dabonetn/Link232-Wifi/zimodem/cbm8bit/src/irc-sw64.bas

!--------------------------------------------------
!- Tuesday, August 17, 2021 9:45:22 AM
!- Import of : 
!- z:\lost+found\irc.prg
!- Commodore 64
!--------------------------------------------------
1 REM IRC64SW  19200B 1.8+
2 REM UPDATED 10/13/2021 12:54A
10 POKE254,PEEK(186):IFPEEK(254)<8THENPOKE254,8
12 GOSUB9200:IFSY=61THENPOKE58,254:CLR
13 IFSY=34THENX=23777:POKEX,170:IFPEEK(X)<>170THENPRINT"<16k":STOP
14 IFSY=227ANDPEEK(51201)=3THENSYS51200
15 OPEN5,2,0,CHR$(BC):IFPEEK(65532)=34THENPOKE56,87:POKE54,87:POKE52,87
17 DIMPP$(25):P$="ok":POKE186,PEEK(254):BA=1200:XB=1200
20 CR$=CHR$(13):PRINTCHR$(14);:GOSUB9200:POKE53280,254:POKE53281,246
30 CO$="{light blue}":IFSY=226THENML=49152:POKE665,73-(PEEK(678)*30):UM=ML+2048:XB=9600
33 IFSY=227THENML=49152:UM=ML+2048
35 IFSY=34THENML=22273:IFPEEK(ML)<>76THENCLOSE5:LOAD"pmlvic.bin",PEEK(254),1:RUN
38 IFSY=34THENPOKE36879,27:CO$=CHR$(31)
40 IFSY=226ANDPEEK(ML+1)<>209THENCLOSE5:LOAD"pml64.bin",PEEK(254),1:RUN
43 IFSY=227ANDPEEK(ML+1)<>209THENCLOSE5:LOAD"pml64.bin",PEEK(254),1:RUN
44 IFSY=227ANDPEEK(51201)<>3THENCLOSE5:LOAD"swiftdrvr.bin",PEEK(254),1:RUN
45 IFSY=226ANDUM>0ANDPEEK(UM+1)<>24THENCLOSE5:LOAD"up9600.bin",PEEK(254),1:RUN
50 IFSY=61THENML=4864:POKE981,15:S8=PEEK(215)AND128:IFS8=128THENSYS30643
60 IFSY=61ANDPEEK(ML+1)<>217THENCLOSE5:LOAD"pml128.bin",PEEK(254),1:RUN
70 IFSY=61ANDS8=128THENXB=2400:CO$=CHR$(159)
80 IFSY=226ANDUM>0THENSYSUM:SYSUM+3:X=PEEK(789):SYSUM+9:IFX=234THENXB=1200
90 IFSY<>34THENPOKE56579,0:REM WHY DOES THIS WORK
100 REM GET THE BAUD RATE
110 P$="a"
120 PRINTCO$;"{clear}{down*2}IRC CHAT v1.5":PRINT"Requires Zimodem firmware 1.8+"
140 PRINT"By Bo Zimmerman (bo@zimmers.net)":PRINT:PRINT
197 REM --------------------------------
198 REM GET STARTED                    !
199 REM -------------------------------
200 UN=PEEK(254):IP$="":CR$=CHR$(13)+CHR$(10)
201 PH=0:PT=0:MV=ML+18
202 PRINT "Initializing modem..."
203 GET#5,A$:IFA$<>""THEN203
205 PRINT#5,CR$;"athz0&p0f0e0";CR$;:GOSUB900:IFP$<>"ok"THEN203
208 GET#5,A$:IFA$<>""THEN208
210 PRINT#5,CR$;"ate0n0r0v1q0";CR$;
220 GOSUB900:IFP$<>"ok"THEN208
230 PRINT#5,"ate0v1x1f3q0s40=250i4";CR$;CHR$(19);
235 GOSUB900:VR=VAL(P$):IFVR<1.8THENPRINT"Zimodem init failed: ";P$:STOP
240 GOSUB900:IFP$<>"ok"THEN203
300 REM GET THE SERVER
310 PRINT:PRINT"{down}Some servers:"
320 PRINT"irc.nlnog.net port 6667, #c-64"
325 PRINT"irc.freenode.net port 6667, #c64friends"
330 PRINT"irc.us.ircnet.net port 6667, #c-64"
350 SE$="":PRINT:PRINT"What is your IRC server host":GOSUB5000:SE$=P$
360 IFSE$=""THENPRINT"I guess you're done then":CLOSE5:STOP
370 PRINT"What is the port":GOSUB5000:PO$=P$:IFVAL(PO$)<=0THENSE$="":GOTO360
380 SE$=SE$+":"+PO$
390 GET#5,A$:IFA$<>""THEN390
400 REM MAKE THE CONNECTION
405 AT$="":IFXB>0ANDBA>0ANDXB<>BATHENAT$="s43="+MID$(STR$(XB),2)
406 GET#5,A$:IFA$<>""THEN406
410 QU$=CHR$(34):PRINT#5,"at"+AT$+"h&d13&m13&m10cp";QU$;SE$;QU$
415 GOSUB900
420 IFLEFT$(P$,8)<>"connect "THENPRINT"Unable to connect to ";SE$;":";P$:GOTO300
425 P=VAL(MID$(P$,8))
427 IFXB<>9600THEN430
428 SYSUM:SYSUM+3:IFPEEK(789)=234THENSYSUM+9:GOTO435
429 BA=XB:POKEUM+19,1:PRINT#5,"at":GOSUB9000:GOSUB9000
430 IFXB<>2400THEN435
431 NP=0:IFPEEK(2614)>0THENNP=20
432 BA=XB:POKE2576,10:POKE2578,PEEK(59490+NP):POKE2579,PEEK(59491+NP)
433 POKE2582,170:POKE2583,1:IFNP>0THENPOKE2582,154
435 PRINT#5,"at":GOSUB9000:GOSUB9000
440 PRINT:PRINT"What is your nickname";:GOSUB5000:NI$=P$:N1=LEN(NI$)
450 IFNI$=""THENPRINT"I guess not.":STOP
460 P$="NICK "+NI$:GOSUB600
470 P$="USER guest 0 * :Joe Anonymous":GOSUB600
490 PRINT"{light green}{reverse on}Connected, wait for MOTD. ? for help{reverse off}";CO$
500 GOTO 1000: REM GO START MAIN LP
598 REM --- TRANSMIT P$ TO THE OPEN SOCKET
600 IFLEN(P$)>0ANDASC(RIGHT$(P$,1))=10THENP$=LEFT$(P$,LEN(P$)-1)
605 OP$=P$:SYSML+9:C8$=MID$(STR$(PEEK(MV+8)),2)::E$="ok":IFVR>3THENE$=C8$
610 PRINT#5,"ats42=";C8$;"t+";QU$;P$;QU$
620 SYSML:IFP$<>E$THENP$=OP$:PRINT"xmit fail";CC$:GOTO600
630 RETURN
698 REM --- GET NEXT FROM SOCKET INTO PP
700 GOSUB930:IFP0<>PANDP0>0THENPRINT"Unexpected packet id: ";P0;"/";P:STOP
710 IFP0=0THENRETURN
720 PP$(PE)=P$:PE=PE+1:IFPE>=25THENPE=0
790 P$="":RETURN
798 REM --- GET P$ FROM SOCKET P
800 E=0:P$="":IFPH>=25THENPH=0
810 IFPH<>PETHENP$=PP$(PH):PH=PH+1:RETURN
820 GOSUB700:IFP0=0THENE=1:RETURN:REM FAIL
830 IFPH<>PETHENP$=PP$(PH):PH=PH+1:RETURN
840 E=1:RETURN
898 REM ---- GET E$ FROM MODEM, OR ERROR
900 E$=""
910 SYSML
920 IFE$<>""ANDP$<>E$THENPRINT"{reverse on}{red}Comm error. Expected ";E$;", Got ";P$;CO$;"{reverse off}"
925 RETURN
928 REM GET PACKET HEADER, SETS P0,P1,P2, RETURNS P0=0 IF NADA
930 SYSML+12:E=0:P0=0:P1=0:P2=0:PR=0:I=0:I0=0:I1=0:CR=0:P4=0:P5=0:C8=0
940 P$="":PRINT#5,CHR$(17);
945 SYSML+6:P0=PEEK(MV+2):P1=PEEK(MV+4):P2=PEEK(MV+6)
950 PL=PEEK(MV+0):CR=PEEK(MV+1):C8=PEEK(MV+8)
960 IFP0>0ANDP2<>C8THEN985
970 IFP1=0THENP$=""
980 IFP0>0ORCR=0THENRETURN
985 SYSML+12:P$=""
990 PRINT"{yellow}PACKET-RETRY";CO$:PRINT#5,"atl":GOTO945
995 PRINT"Expected ";E$;", got ";A$:STOP
998 REM THE MAIN LOOP
1000 GETA$:IFA$<>""THEN3000
1020 GOSUB800:IFP$=""THEN1000
1030 MS$="":MC$="":MA$="":I=1:LP$=P$
1040 IFMID$(P$,1,1)<>":"THEN1100
1050 IFI>LEN(P$)THEN1100
1060 IFMID$(P$,I,1)<>" "THENI=I+1:GOTO1050
1070 MS$=MID$(P$,1,I-1):P$=MID$(P$,I+1)
1100 I=1:IFP$=""THEN1000
1110 IFI>LEN(P$)THEN1200
1120 IFMID$(P$,I,1)<>" "THENI=I+1:GOTO1110
1130 MC$=MID$(P$,1,I-1):P$=MID$(P$,I+1)
1200 MA$=P$:IFMC$=""THEN1000
1210 A=ASC(MID$(MC$,1,I)):IFA<48ORA>57THEN1300
1220 IFLEN(MC$)>1ANDMID$(MC$,1,1)="0"THENMC$=MID$(MC$,2):GOTO1220
1230 C=VAL(MC$):IFC>430ANDC<460THENPRINT"Bad Nick given(";C;") : "+MA$:GOTO440
1240 IFC>400THENPRINT"Error: "+MA$:GOTO1000
1250 IFLEN(MA$)>N1+1ANDMID$(MA$,1,N1)=NI$THENMA$=MID$(MA$,LEN(NI$)+2)
1260 PRINT MA$:GOTO1000
1300 REM CMDS
1310 IFMC$="PING"THEN1400
1320 IFMC$="MODE"THEN1000
1330 IFMC$="PRIVMSG"THEN2000
1340 IFMC$="VERSION"THEN2100
1350 IFMC$="QUIT"THEN2200
1360 IFMC$="JOIN"THEN2300
1370 IFMC$="PONG"THEN1000
1390 REM
1397 PRINTLP$:GOTO1000
1398 PRINT"Unknown: '"+MC$+"' '"+MA$+"'"
1399 GOTO1000
1400 REM ...
1410 OM$=MA$:P$="PONG :"+MA$:GOSUB600:E$="":GOTO1000
2000 I=1:IFMA$=""THEN1000
2010 IFMID$(MA$,I,2)=" :"THEN2050
2020 I=I+1:GOTO2010
2050 GOSUB2900
2090 PRINT"{reverse on}";MS$;"{reverse off}: ";MID$(MA$,I+2):GOTO1000
2100 PRINT"{reverse on}";LP$;"{reverse off}":GOTO1000
2200 GOSUB2900:PRINT"{pink}{reverse on}";MS$;" has left the channel.{reverse off}";CO$:GOTO1000
2300 GOSUB2900:PRINT"{light green}{reverse on}";MS$;" has joined the channel.{reverse off}";CO$:GOTO1000
2900 II=2
2910 IFII>LEN(MS$)THENII=LEN(MS$):GOTO2950
2920 IFMID$(MS$,II,1)="!"THENII=II-1:GOTO2950
2930 II=II+1:GOTO2910
2950 MS$=MID$(MS$,1,II):RETURN
3000 IFA$=CHR$(13)THEN1000
3010 PRINT"{reverse on}{pink}Stream paused. Enter ? for help.{reverse off}"
3020 IFOM$<>""THENP$="PING "+OM$:GOSUB600
3090 PRINTCO$;">{reverse on} {reverse off}{left}";:IN$="":IT=TI+1000:GOTO3200
3100 IFTI>ITTHENPRINT"{reverse on}{red}Cancelled{reverse off}{pink}":PRINT:GOTO1000
3150 GETA$:IFA$=""THEN3100
3170 IT=TI+1000
3200 IFA$=CHR$(13)THEN3300
3210 IFA$<>CHR$(20)ORLEN(IN$)=0THEN3230
3220 IN$=LEFT$(IN$,LEN(IN$)-1):PRINT" {left*2} {left}{reverse on} {reverse off}{left}";:GOTO3100
3230 A=ASC(A$):IFA<32OR(A>95ANDA<193)ORA>218THEN3100
3240 IN$=IN$+A$:PRINTA$;"{reverse on} {reverse off}{left}";:GOTO3100
3300 IFIN$=""THENPRINT" ":PRINT:GOTO1000
3305 IFIN$="?"THENPRINT" ":GOTO3400
3310 IFMID$(IN$,1,1)="/"THENIN$=MID$(IN$,2):GOTO3500
3320 IFCC$=""THENPRINT:PRINT"{reverse on}{red}No Channel Selected! Try ?{reverse off}";CO$:GOTO1000
3330 P$="PRIVMSG "+CC$+" :"+IN$
3340 GOSUB600:PRINT" ":PRINT"{reverse on}";NI$;"{reverse off}: ";IN$
3350 E$="":PRINT:GOTO1000
3400 PRINTCO$;"{reverse off}------------------------------"
3410 PRINT"{reverse on}{purple}/join #c-64{reverse off} ";CO$;"Change channels."
3420 PRINT"{reverse on}{purple}/quit{reverse off} ";CO$;"Logout and exit."
3430 REMPRINT"{reverse on}{purple}/list{reverse off} ";CO$;"List channels."
3440 REMPRINT"{reverse on}{purple}/who mask*{reverse off} ";CO$;"User info."
3480 PRINT"{reverse on}{purple}Anything else{reverse off} ";CO$;"Send message"
3490 PRINTCO$;"{reverse off}------------------------------":GOTO1000
3500 X=0:FORI=2TOLEN(IN$):IFX=0ANDMID$(IN$,I,1)=" "THENX=I
3510 NEXT:A$="":IFX>1THENA$=MID$(IN$,X+1):IN$=MID$(IN$,1,X-1)
3520 PRINT
3530 IFIN$="join"THEN4000
3540 IFIN$="quit"THENP$="QUIT :":GOSUB600:GOTO9100
3550 IFIN$="list"THENP$="LIST":GOSUB600:GOTO1000
3560 IFIN$="who"THENP$="WHO :"+AA$:GOSUB600:GOTO1000
3999 PRINT"{reverse on}{red}Unknown Command: ";IN$;". Try ?{reverse off}";CO$:GOTO1000
4000 PRINT"Joining ";QU$;A$;QU$:AA$=A$
4100 P$="JOIN :"+AA$:GOSUB600
4120 E$="":CC$=AA$:GOTO1000
5000 PRINT"? {reverse on} {reverse off}{left}";:P$=""
5010 GETA$:IFA$=""THEN5010
5020 IFA$=CHR$(13)THENPRINT" {left}":RETURN
5030 IFA$<>CHR$(20)THENPRINTA$;"{reverse on} {reverse off}{left}";:P$=P$+A$:GOTO5010
5040 IFP$=""THEN5010
5050 P$=LEFT$(P$,LEN(P$)-1):PRINT" {left*2} {left}{reverse on} {reverse off}{left}";:GOTO5010
9000 TT=TI+100
9010 SYSML+12:IFTI<TTTHEN9010
9020 RETURN
9100 PRINT#5,"atz":GOSUB9000:GOSUB9000:CLOSE5:END
9200 SY=PEEK(65532):BC=8
9210 IFSY<>226THEN9240
9220 X=PEEK(56834):POKE56834,X+1:IFPEEK(56834)<>X+1THEN9240
9230 BC=15:SY=227:POKE56834,X:RETURN
9240 PRINTCHR$(14);"Requires a C64 with SwiftLink/Link232":STOP
50000 OPEN5,2,0,CHR$(8)
50010 GET#5,A$:IFA$<>""THENPRINTA$;
50020 GETA$:IFA$<>""THENPRINT#5,A$;
50030 GOTO 50010
55555 U=8:F$="irc":OPEN1,U,15,"s0:"+F$:CLOSE1:SAVEF$,U:VERIFYF$,U
