dabonetn/Link232-Wifi/zimodem/zimodem/zprint.ino

/*
   Copyright 2020-2020 Bo Zimmerman

   Licensed under the Apache License, Version 2.0 (the "License");
   you may not use this file except in compliance with the License.
   You may obtain a copy of the License at

     http://www.apache.org/licenses/LICENSE-2.0

   Unless required by applicable law or agreed to in writing, software
   distributed under the License is distributed on an "AS IS" BASIS,
   WITHOUT WARRANTIES OR CONDITIONS OF ANY KIND, either express or implied.
   See the License for the specific language governing permissions and
   limitations under the License.
*/

size_t ZPrint::writeStr(char *s)
{
  if(outStream != null)
  {
    int len=strlen(s);
    outStream->write((uint8_t *)s,len);
    if(logFileOpen)
    {
      for(int i=0;i<len;i++)
        logSocketOut(s[i]);
    }
    return len;
  }
  return 0;
}

char *ZPrint::getLastPrinterSpec()
{
  if(lastPrinterSpec==0)
    return "";
  return lastPrinterSpec;
}

void ZPrint::setLastPrinterSpec(const char *spec)
{
  if(lastPrinterSpec != 0)
    free(lastPrinterSpec);
  lastPrinterSpec = 0;
  if((spec != 0) && (*spec != 0))
  {
    int newLen = strlen(spec);
    lastPrinterSpec = (char *)malloc(newLen + 1);
    strcpy(lastPrinterSpec,spec);
  }
}


int ZPrint::getTimeoutDelayMs()
{
  return timeoutDelayMs;
}

void ZPrint::setTimeoutDelayMs(int ms)
{
  if(ms > 50)
    timeoutDelayMs = ms;
}

size_t ZPrint::writeChunk(char *s, int len)
{
  char buf[25];
  sprintf(buf,"%x\r\n",len);
  writeStr(buf);
  outStream->write((uint8_t *)s,len);
  if(logFileOpen)
  {
    for(int i=0;i<len;i++)
      logSocketOut(s[i]);
  }
  writeStr("\r\n");
  return len+strlen(buf)+4;
}

void ZPrint::announcePrintJob(const char *hostIp, const int port, const char *req)
{
  logPrintfln("Print Request to host=%s, port=%d",hostIp,port);
  debugPrintf("Print Request to host=%s, port=%d\n",hostIp,port);
  logPrintfln("Print Request is /%s",req);
  debugPrintf("Print Request is /%s\n",req);
}

ZResult ZPrint::switchToPostScript(char *prefix)
{
  if((lastPrinterSpec==0)
  ||(strlen(lastPrinterSpec)<=5)
  ||(lastPrinterSpec[1]!=':'))
    return ZERROR;
  char *workBuf = (char *)malloc(strlen(lastPrinterSpec) +1);
  strcpy(workBuf, lastPrinterSpec);
  
  char *hostIp;
  char *req;
  int port;
  bool doSSL;
  if(!parseWebUrl((uint8_t *)workBuf+2,&hostIp,&req,&port,&doSSL))
  {
    free(workBuf);
    return ZERROR;
  }
  payloadType = RAW;
  announcePrintJob(hostIp,port,req);
  ZResult result;
  if(pinSupport[pinRTS])
    s_pinWrite(pinRTS, rtsInactive);
  yield();
  wifiSock = new WiFiClientNode(hostIp,port,doSSL?FLAG_SECURE:0);
  wifiSock->setNoDelay(false); // we want a delay in this case
  outStream = wifiSock;
  result = finishSwitchTo(hostIp, req, port, doSSL);
  if(result == ZERROR)
  {
    outStream = null;
    delete wifiSock;
    wifiSock = null;
  }
  yield();
  if(pinSupport[pinRTS])
    s_pinWrite(pinRTS, rtsActive);
  if((result != ZERROR)
  &&(prefix != 0)
  &&(strlen(prefix)>0))
  {
    writeChunk(prefix,strlen(prefix));
    serialIncoming();
  }
  free(workBuf);
  return result;
}

ZResult ZPrint::switchTo(char *vbuf, int vlen, bool petscii)
{
  char *workBuf = (char *)malloc(vlen+1);
  strcpy(workBuf, vbuf);
  if(petscii)
  {
    for(int i=0;i<vlen;i++)
      workBuf[i] = petToAsc(workBuf[i]);
  }
  bool newUrl = true;
  if((vlen <= 2)||(workBuf[1]!=':'))
  {
    if((lastPrinterSpec==0)
    ||(strlen(lastPrinterSpec)<=5)
    ||(lastPrinterSpec[1]!=':'))
    {
      free(workBuf);
      return ZERROR;
    }
    if((vlen == 1)
    &&(strchr("parPAR",workBuf[0])!=0))
      lastPrinterSpec[0]=workBuf[0];
    free(workBuf);
    workBuf = (char *)malloc(strlen(lastPrinterSpec) +1);
    strcpy(workBuf, lastPrinterSpec);
    vlen=strlen(workBuf);
    newUrl = false;
  }
  
  switch(workBuf[0])
  {
  case 'P': case 'p': 
    payloadType = PETSCII;
    break;
  case 'A': case 'a': 
    payloadType = ASCII;
    break;
  case 'R': case 'r': 
    payloadType = RAW;
    break;
  default:
    free(workBuf);
    return ZERROR;
  }
  char *hostIp;
  char *req;
  int port;
  bool doSSL;
  if(!parseWebUrl((uint8_t *)workBuf+2,&hostIp,&req,&port,&doSSL))
  {
    free(workBuf);
    return ZERROR;
  }
  if(newUrl)
    setLastPrinterSpec(vbuf);
  
  wifiSock = new WiFiClientNode(hostIp,port,doSSL?FLAG_SECURE:0);
  wifiSock->setNoDelay(false); // we want a delay in this case
  outStream = wifiSock;
  announcePrintJob(hostIp,port,req);
  ZResult result = finishSwitchTo(hostIp, req, port, doSSL);
  free(workBuf);
  if(result == ZERROR)
    delete wifiSock;
  return result;
}

ZResult ZPrint::finishSwitchTo(char *hostIp, char *req, int port, bool doSSL)
{
  if((wifiSock != null) && (!wifiSock->isConnected()))
    return ZERROR;
  char portStr[10];
  sprintf(portStr,"%d",port);
  // send the request and http headers:
  sprintf(pbuf,"POST /%s HTTP/1.1\r\n",req);
  writeStr(pbuf);
  writeStr("Transfer-Encoding: chunked\r\n");
  writeStr("Content-Type: application/ipp\r\n");
  sprintf(pbuf,"Host: %s:%d\r\n",hostIp,port);
  writeStr(pbuf);
  writeStr("Connection: Keep-Alive\r\n");
  writeStr("User-Agent: Zimodem\r\n");
  writeStr("Accept-Encoding: gzip,deflate\r\n");
  writeStr("\r\n");
  outStream->flush();
  // send the ipp header
  if((wifiSock != null)&&(!wifiSock->isConnected()))
    return ZERROR;
  
  char jobChar1 = '0' + (jobNum / 10);
  char jobChar2 = '0' + (jobNum % 10);
  if(++jobNum>94)
    jobNum=0;
  //                                version  operatid  reqid------------------ attribtabid
  sprintf(pbuf,"%c%c%c%c%c%c%c%c%c",0x01,0x01,0x00,0x02,0x00,0x00,0x00,jobNum+1,0x01);
  writeChunk(pbuf,9);
  sprintf(pbuf,"%c%c%cattributes-charset%c%cutf-8",0x47,0x00,0x12,0x00,0x05);
  writeChunk(pbuf,28);
  sprintf(pbuf,"%c%c%cattributes-natural-language%c%cen-us",0x48,0x00,0x1b,0x00,0x05);
  writeChunk(pbuf,37);
  
  int urllen = strlen(hostIp) + strlen(req)+ strlen(portStr)+9;
  sprintf(pbuf,"%c%c%cprinter-uri%c%chttp://%s:%s/%s",0x45,0x00,0x0b,0x00,urllen,hostIp,portStr,req);
  writeChunk(pbuf,urllen+16);
  sprintf(pbuf,"%c%c%crequesting-user-name%c%czimodem",0x42,0x00,0x14,0x00,0x07);
  writeChunk(pbuf,32);
  sprintf(pbuf,"%c%c%cjob-name%c%czimodem-j%c%c",0x42,0x00,0x08,0x00,0x0b,jobChar1,jobChar2);
  writeChunk(pbuf,24);
  sprintf(pbuf,"%c%c%c%ccopies%c%c%c%c%c%c",0x02,0x21,0x00,0x06,0x00,0x04,0x00,0x00,0x00,0x01);
  writeChunk(pbuf,16);
  sprintf(pbuf,"%c%c%corientation-requested%c%c%c%c%c%c",0x23,0x00,0x15,0x00,0x04,0x00,0x00,0x00,0x03);
  writeChunk(pbuf,30);
  sprintf(pbuf,"%c%c%coutput-mode%c%cmonochrome%c",0x44,0x00,0x0b,0x00,0x0a,     0x03);
  writeChunk(pbuf,27);
  outStream->flush();
  if((wifiSock != null)&&(!wifiSock->isConnected()))
    return ZERROR;
  checkOpenConnections();
  checkBaudChange();
  pdex=0;
  coldex=0;
  lastNonPlusTimeMs = 0;
  plussesInARow=0;
  currentExpiresTimeMs = millis()+5000;
  currMode=&printMode;
  return ZIGNORE;
}

void ZPrint::serialIncoming()
{
  if(HWSerial.available() > 0)
  {
    while(HWSerial.available() > 0)
    {
      uint8_t c=HWSerial.read();
      logSerialIn(c);
      if((c==commandMode.EC)
      &&(plussesInARow<3)
      &&((plussesInARow>0)||((millis()-lastNonPlusTimeMs)>900)))
      {
        plussesInARow++;
        continue;
      }
      else
      {
        if(plussesInARow > 0)
        {
          for(int i=0;i<plussesInARow;i++)
            pbuf[pdex++]=commandMode.EC;
          plussesInARow=0;
        }
        lastNonPlusTimeMs=millis();
      }
      
      if(payloadType == PETSCII)
        c=petToAsc(c);
      if(payloadType != RAW)
      {
        if(c==0)
          continue;
        else
        if(c<32)
        {
          if((c=='\r')||(c=='\n'))
          {
            coldex=0;
          }
        }
        else
        {
          coldex++;
          if(coldex > 80)
          {
            pbuf[pdex++]='\n';
            pbuf[pdex++]='\r';
            coldex=1;
          }
          else
          if((lastC == '\n')&&(lastLastC!='\r'))
              pbuf[pdex++]='\r';
          else
          if((lastC == '\r')&&(lastLastC!='\n'))
              pbuf[pdex++]='\n';
        }
      }
      pbuf[pdex++]=(char)c;
      lastLastC=lastC;
      lastC=c;
      if(pdex>=250)
      {
        if(((wifiSock!=null)&&(wifiSock->isConnected()))
        ||((wifiSock==null)&&(outStream!=null)))
        {
          writeChunk(pbuf,pdex);
          //wifiSock->flush();
        }
        pdex=0;
      }
    }
    if(plussesInARow == 3)
      currentExpiresTimeMs = millis()+900;
    else
      currentExpiresTimeMs = millis()+timeoutDelayMs;
  }
}

void ZPrint::switchBackToCommandMode(bool error)
{
  if((wifiSock != null)||(outStream!=null))
  {
    if(error)
      commandMode.sendOfficialResponse(ZERROR);
    else
      commandMode.sendOfficialResponse(ZOK);
    if(wifiSock != null)
      delete wifiSock;
  }
  wifiSock = null;
  outStream = null;
  currMode = &commandMode;
}

void ZPrint::loop()
{
  if(((wifiSock==null)&&(outStream==null))
  || ((wifiSock!=null)&&(!wifiSock->isConnected())))
  {
    debugPrintf("No printer connection\n");
    switchBackToCommandMode(true);
  }
  else
  if(millis()>currentExpiresTimeMs)
  {
    debugPrintf("Time-out in printing\n");
    if(pdex > 0)
      writeChunk(pbuf,pdex);
    writeStr("0\r\n\r\n");
    outStream->flush();
    switchBackToCommandMode(false);
  }
  checkBaudChange();
}
