dabonetn/Link232-Wifi/zimodem/cbm8bit/src/x-xfer128.asm

*= $C800
;.D X-XFER128.BIN
; Requires modem on channel 5, file on channel 2
        JMP SENDFIL
        JMP RECVCHK
        JMP SENDFIL
        JMP RECVCRC
PRINT2
        NOP
        ;OPEN1,8,15,"S0:X-XFER 1300,ML1300X":CLOSE1:SAVE"ML1300X",8:STOP
;**********
;CRC TABLES
;**********
CRCLSB
        BYTE 0,33,66,99,132,165,198,231
        BYTE 8,41,74,107,140,173,206,239
        BYTE 49,16,115,82,181,148,247,214
        BYTE 57,24,123,90,189,156,255,222
        BYTE 98,67,32,1,230,199,164,133
        BYTE 106,75,40,9,238,207,172,141
        BYTE 83,114,17,48,215,246,149,180
        BYTE 91,122,25,56,223,254,157,188
        BYTE 196,229,134,167,64,97,2,35
        BYTE 204,237,142,175,72,105,10,43
        BYTE 245,212,183,150,113,80,51,18
        BYTE 253,220,191,158,121,88,59,26
        BYTE 166,135,228,197,34,3,96,65
        BYTE 174,143,236,205,42,11,104,73
        BYTE 151,182,213,244,19,50,81,112
        BYTE 159,190,221,252,27,58,89,120
        BYTE 136,169,202,235,12,45,78,111
        BYTE 128,161,194,227,4,37,70,103
        BYTE 185,152,251,218,61,28,127,94
        BYTE 177,144,243,210,53,20,119,86
        BYTE 234,203,168,137,110,79,44,13
        BYTE 226,195,160,129,102,71,36,5
        BYTE 219,250,153,184,95,126,29,60
        BYTE 211,242,145,176,87,118,21,52
        BYTE 76,109,14,47,200,233,138,171
        BYTE 68,101,6,39,192,225,130,163
        BYTE 125,92,63,30,249,216,187,154
        BYTE 117,84,55,22,241,208,179,146
        BYTE 46,15,108,77,170,139,232,201
        BYTE 38,7,100,69,162,131,224,193
        BYTE 31,62,93,124,155,186,217,248
        BYTE 23,54,85,116,147,178,209,240
;
CRCMSB
        BYTE 0,16,32,48,64,80,96,112
        BYTE 129,145,161,177,193,209,225,241
        BYTE 18,2,50,34,82,66,114,98
        BYTE 147,131,179,163,211,195,243,227
        BYTE 36,52,4,20,100,116,68,84
        BYTE 165,181,133,149,229,245,197,213
        BYTE 54,38,22,6,118,102,86,70
        BYTE 183,167,151,135,247,231,215,199
        BYTE 72,88,104,120,8,24,40,56
        BYTE 201,217,233,249,137,153,169,185
        BYTE 90,74,122,106,26,10,58,42
        BYTE 219,203,251,235,155,139,187,171
        BYTE 108,124,76,92,44,60,12,28
        BYTE 237,253,205,221,173,189,141,157
        BYTE 126,110,94,78,62,46,30,14
        BYTE 255,239,223,207,191,175,159,143
        BYTE 145,129,177,161,209,193,241,225
        BYTE 16,0,48,32,80,64,112,96
        BYTE 131,147,163,179,195,211,227,243
        BYTE 2,18,34,50,66,82,98,114
        BYTE 181,165,149,133,245,229,213,197
        BYTE 52,36,20,4,116,100,84,68
        BYTE 167,183,135,151,231,247,199,215
        BYTE 38,54,6,22,102,118,70,86
        BYTE 217,201,249,233,153,137,185,169
        BYTE 88,72,120,104,24,8,56,40
        BYTE 203,219,235,251,139,155,171,187
        BYTE 74,90,106,122,10,26,42,58
        BYTE 253,237,221,205,189,173,157,141
        BYTE 124,108,92,76,60,44,28,12
        BYTE 239,255,207,223,175,191,143,159
        BYTE 110,126,78,94,46,62,14,30
;****************
;VARIABLE STORAGE
;****************
BUFFER = $CEFD
BUFFER3 = $CF00
ENDBUF = $CF80
CRCBUF = $CF81
ACK = $06
CAN = $18
EOT = $04
NAK = $15
SOH = $01
CNAK = $43
PAD = $1A
OTH = $02


ABORTFLAG = $FB
UPDN = $FE
XTYPE = $FF
FREEKEY = $FA


; KERNAL JUMPS
JSRFAR = $02CD
LOCJSRFAR = $1BE0
FETCH = $02A2

; C128 Specific Locations
TIMEHB = $A0
TIMEMB = $A1
TIMELB = $A2
SHFLAG = $D3
RIDBS = $0A18 ; index to first char in input buffer
RIDBE = $0A19 ; index to last char in input buffer
RODBS = $0A1A ; index to first char in output buffer
RODBE = $0A1B ; index to last char in output buffer
KEYINDEX = $D0
CASSSYNCCT = $96
STATUS = $90
RIBUF = $C8

;***************
;VARIABLE MEMORY
;***************
BLOCK             BYTE 0
GOOD              BYTE 0
ERRORS            BYTE 0
ABORT             BYTE 0
TIMEOUTS          BYTE 0
BUFBIT            BYTE 0
BUFSIZE           BYTE 0
CHECKSM           BYTE 0
CRC               BYTE 0,0
CLOCK             BYTE 0
IOSTAT            BYTE 0
;*************
;MISC ROUTINES
;*************
GOGOFAR
        LDA #$00
        STA $FF00
        JSR JSRFAR
        LDA #$3F
        STA $FF00
        RTS

PREFAR
        STA $06
        STX $07
        STY $08
        LDA LOCJSRFAR
        CMP GOGOFAR
        BEQ PREFAR3 
        LDX #$FF
PREFAR2
        INX
        LDA GOGOFAR,X
        STA LOCJSRFAR,X
        CPX #$10
        BCC PREFAR2
PREFAR3 
        LDA #$0F
        STA $02
        LDA #$FF
        STA $03
        RTS

GOFAR
        STA $04
        JSR LOCJSRFAR
        LDX $07
        LDY $08
        LDA $06
        RTS

CHKIN   
        JSR PREFAR
        LDA #$C6
        JMP GOFAR
        
CHKOUT
        JSR PREFAR
        LDA #$C9
        JMP GOFAR
CLRCH
        JSR PREFAR
        LDA #$CC
        JMP GOFAR
BSOUT
        JSR PREFAR
        LDA #$D2
        JMP GOFAR
SETTIM
        JSR PREFAR
        LDA #$DB
        JMP GOFAR
GETIN
        JSR PREFAR
        LDA #$E4
        JMP GOFAR

GETDD01
        TYA
        PHA
        TXA
        PHA
        LDA #$01
        STA $03
        LDA #$DD
        STA $04
        LDA #$03
        STA $02AA
        LDY #$00
        LDX #$00
        JSR FETCH
        STA $06
        PLA
        TAX
        PLA
        TAY
        LDA $06
        CMP #$00
        RTS      

CLEAR
        LDA #$00
        STA BLOCK
        STA GOOD
        STA ERRORS
        STA ABORT
        STA BUFBIT
        STA CHECKSM
        STA CRC
        STA CRC+1
        STA TIMEOUTS
        STA IOSTAT
        RTS
RETIME
        LDA #$00
        TAX
        TAY
        JMP SETTIM
CHECKTIME
        LDA #$00
        STA CLOCK
        LDA TIMEMB
        CMP #$03
        BCS BADTIME
        RTS
BADTIME
        INC TIMEOUTS
        INC CLOCK
        JMP RETIME
CHECKABORT
        LDA SHFLAG
        CMP #$02
        BEQ ABORTED
        JSR GETDD01
        and #$10
        beq ABORTED
        RTS
ABORTED
        LDA #$01
        STA ABORT
        JMP CLRCH
ERRFLUSH
        INC ERRORS
FLUSHBUF
        LDY #$00
        TYA
FLUSHLP
        STA BUFFER,Y
        INY
        CPY #$85
        BCC FLUSHLP
MINFLUSH
        LDA RIDBS
        STA RIDBE
        LDA RODBS
        STA RODBE
        LDA #$00
        STA KEYINDEX
        STA BUFBIT
        STA GOOD
        JSR RETIME
        RTS
PAAS
        JSR RETIME
PAS1
        LDA TIMELB
        CMP #$05
        BNE PAS1
        RTS
GETKEY
        TYA
        PHA
        LDA RIDBS
        CMP RIDBE
        BEQ NOKEY
        LDY RIDBE
        LDA (RIBUF),Y
        STA FREEKEY
        INC RIDBE
        LDA #$01
        STA CASSSYNCCT
        PLA
        TAY
        RTS
NOKEY
        LDA #$00
        STA CASSSYNCCT
        STA FREEKEY
        PLA
        TAY
        RTS
;*******************
;CHECK BLOCK ROUTINE
;*******************
CHKBLK
        LDA XTYPE
        BNE CRCCHK
        LDY #$00
        STY CHECKSM
CHKCHK
        LDA BUFFER3,Y
        CLC
        ADC CHECKSM
        STA CHECKSM
        INY
        CPY #$80
        BCC CHKCHK
        RTS
CRCCHK
        LDY #$00
        STY CRC
        STY CRC+1
CRCCLP
        LDA BUFFER3,Y
        EOR CRC
        TAX
        LDA CRCMSB,X
        EOR CRC+1
        STA CRC
        LDA CRCLSB,X
        STA CRC+1
        INY
        CPY #$80
        BNE CRCCLP
        RTS
;*********************
;RECEIVE A XMODEM FILE
;*********************
RECVCHK
        LDA #$00
        STA XTYPE
        LDA #$84
        STA BUFSIZE
        JMP RCVBEGIN
RECVCRC
        LDA #$01
        STA XTYPE
        LDA #$85
        STA BUFSIZE
RCVBEGIN
        LDA #$01
        STA UPDN
        JSR CLEAR
        JSR FLUSHBUF
        INC BLOCK
        LDX #$05
        JSR CHKOUT
        LDA XTYPE
        BNE CXNAK
        LDA #NAK
        JSR BSOUT
        JMP RECVLP
CXNAK
        LDA #CNAK
        JSR BSOUT
RECVLP
        LDA ERRORS
        CMP #$0E
        BCC R2;**TOO MANY ERRS
CANCEL
        LDA #$01
        STA ABORT
R2      JSR CHECKABORT
        JSR CHECKTIME
        LDA ABORT
        BEQ ARECVN
        JMP ABORTXMODEM
RCVDONE
        JMP EXITRCV
ARECVN
        LDA BLOCK
        CMP #$01
        BNE NEXTR
        LDA TIMEOUTS
        CMP #$02
        BNE NEXTR
        JMP CANCEL
NEXTR
        LDA CLOCK
        BEQ NOCLOCK
        JMP NORBORT
NOCLOCK
        LDX #$05
        JSR CHKIN
        LDA BUFFER
        CMP #CAN
        BEQ CANCEL
        CMP #EOT
        BEQ RCVDONE
        JSR GETKEY
        LDA CASSSYNCCT
        BEQ RECVLP
        JSR RETIME
        LDY BUFBIT
        LDA FREEKEY
        STA BUFFER,Y
        INC BUFBIT
        INY
        CPY BUFSIZE
        BCC RECVLP
;**** CHECK THE BLOCK ****
        JSR PAAS
        LDA BUFFER
        CMP #EOT
        BEQ RCVDONE
        CMP #CAN
        BEQ CANCEL
        CMP #OTH
        BEQ CHKREST
        CMP #SOH
        BEQ CHKREST
        JMP CONRCV
CHKREST
        LDA BUFFER+1
        CMP BLOCK
        BNE CONRCV
        EOR #$FF
        CMP BUFFER+2
        BNE CONRCV
        JSR CHKBLK
        LDA XTYPE
        BNE CRCDO
        LDA CHECKSM
        CMP ENDBUF
        BEQ GOODIE
        JMP CONRCV
CRCDO
        LDA ENDBUF
        CMP CRC
        BNE CONRCV
        LDA CRCBUF
        CMP CRC+1
        BNE CONRCV
GOODIE
        LDA #$01
        STA GOOD
;**** WRITE OR NAK BLOCK ****
CONRCV
        LDA GOOD
        BEQ NORGOOD
        JSR CLRCH
        LDX #$02
        JSR CHKOUT
        LDY #$00
WRITELP
        LDA BUFFER3,Y
        JSR BSOUT
        INY
        CPY #$80
        BCC WRITELP
        JSR FLUSHBUF
        JSR CLRCH
        LDA #$2D
        JSR BSOUT
        LDX #$05
        JSR CHKOUT
        LDA #ACK
        JSR BSOUT
        JSR CLRCH
        INC BLOCK
        JMP RECVLP
NORGOOD
        LDA ABORT
        BEQ NORBORT
        JMP ABORTXMODEM
NORBORT
        JSR FLUSHBUF
        JSR CLRCH
        LDA #$3A
        JSR BSOUT
        LDX #$05
        JSR CHKOUT
        LDA XTYPE
        BNE CNKK
NAKK
        LDA #NAK
        JSR BSOUT
        JMP CONAK
CNKK
        LDA BLOCK
        CMP #$02
        BCS NAKK
        LDA #CNAK
        JSR BSOUT
CONAK
        INC ERRORS
        JSR CLRCH
        JMP RECVLP
;****** ALL DONE ******
EXITRCV
        JSR CLRCH
        LDX #$05
        JSR CHKOUT
        LDA #ACK
        JSR BSOUT
        JMP EXITXMODEM
ABORTXMODEM
        LDA #$01
        STA ABORT
        JSR CLRCH
        LDX #$05
        JSR CHKOUT
        LDA #CAN
        JSR BSOUT
        JSR BSOUT
        JSR BSOUT
EXITXMODEM
        LDX ABORT
        JSR CLEAR
        STX ABORT
        JSR FLUSHBUF
        LDA #$00
        STA XTYPE
        STA UPDN
        JSR CLRCH
        LDA #$2A
        JSR BSOUT
        LDA ABORT
        STA ABORTFLAG
        RTS
;******************
;SEND A XMODEM FILE
;******************
SENDFIL
        LDA #$00
        STA UPDN
        JSR CLEAR
        JSR FLUSHBUF
        JSR SNDSCRC
        JMP SNDSTART
SNDSCHK
        LDA #$00
        STA XTYPE
        LDA #$84
        STA BUFSIZE
        RTS
SNDSCRC
        LDA #$01
        STA XTYPE
        LDA #$85
        STA BUFSIZE
        RTS
SNDBUILD
        LDX #$02
        JSR CHKIN
        LDY #$00
        STY IOSTAT
SREAD
        JSR GETIN
        STA BUFFER3,Y
        LDA STATUS
        STA IOSTAT
        BNE PADBUF
        INY
        CPY #$80
        BCC SREAD
        JMP SND2
PADBUF
        INY
        INY
        CPY #$80
        BCC PAD2
PAD2
        LDA #PAD
        STA BUFFER3,Y
        INY
        CPY #$80
        BCC PAD2
SND2
        LDA #SOH
        STA BUFFER
        LDA BLOCK
        STA BUFFER+1
        EOR #$FF
        STA BUFFER+2
;**** BUILD CHECKSUMS ****
        JSR CHKBLK
        LDA CHECKSM
        STA ENDBUF
        LDA XTYPE
        BEQ SNDCONT
        LDA CRC
        STA ENDBUF
        LDA CRC+1
        STA CRCBUF
;***** SEND THE BLOCK *****
SNDCONT
        JSR MINFLUSH
        JSR CLRCH
        LDX #$05
        JSR CHKOUT
        LDY #$00
        STY BUFBIT
SENDLOOP
        LDA BUFFER,Y
        JSR BSOUT
        LDY BUFBIT
        INY
        STY BUFBIT
        CPY BUFSIZE
        BCC SENDLOOP
SNDSTART
        JSR CLRCH
        LDX #$05
        JSR CHKIN
        JSR RETIME
SENDWAIT
        JSR CHECKABORT
        JSR CHECKTIME
        JSR GETIN
        CMP #NAK
        BEQ SNDCHK
        CMP #CNAK
        BEQ SNDCRC
        CMP #CAN
        BEQ SNDABORT
        CMP #ACK
        BEQ NEXTBLOCK
        LDA ERRORS
        CMP #$0E
        BEQ SNDABORT
        LDA ABORT
        BNE SNDABORT
        LDA CLOCK
        BNE SENDERR
        JMP SENDWAIT
;****** MISC SEND ROUTINES ******
SNDABORT
        JMP ABORTXMODEM
SNDCRC
        JSR SNDSCRC
        JMP SENDRE
SNDCHK
        JSR SNDSCHK
SENDRE
        LDA BLOCK
        BEQ NEXTBLOCK
SENDERR
        INC ERRORS
        JSR CLRCH
        LDA #$3A
        JSR BSOUT
        JSR PAAS
        JMP SNDCONT
NEXTBLOCK
        INC BLOCK
        JSR CLRCH
        LDA #$2D
        JSR BSOUT
        LDA IOSTAT
        BEQ NXTGO
        LDX #$05
        JSR CHKOUT
        LDY #$00
EOPL
        LDA #EOT
        JSR BSOUT
        INY
        CPY #$85
        BNE EOPL
        JMP EXITXMODEM
NXTGO
        JSR PAAS
        JSR FLUSHBUF
        JMP SNDBUILD
