dabonetn/Link232-Wifi/zimodem/zimodem/proto_http.ino

/*
   Copyright 2016-2019 Bo Zimmerman

   Licensed under the Apache License, Version 2.0 (the "License");
   you may not use this file except in compliance with the License.
   You may obtain a copy of the License at

     http://www.apache.org/licenses/LICENSE-2.0

   Unless required by applicable law or agreed to in writing, software
   distributed under the License is distributed on an "AS IS" BASIS,
   WITHOUT WARRANTIES OR CONDITIONS OF ANY KIND, either express or implied.
   See the License for the specific language governing permissions and
   limitations under the License.
*/
bool parseWebUrl(uint8_t *vbuf, char **hostIp, char **req, int *port, bool *doSSL)
{
  *doSSL = false;
  if(strstr((char *)vbuf,"http:")==(char *)vbuf)
    vbuf = vbuf + 5;
  else
  if(strstr((char *)vbuf,"https:")==(char *)vbuf)
  {
    vbuf = vbuf + 6;
    *doSSL = true;
  }
  while(*vbuf == '/')
    vbuf++;

  *port= (*doSSL) ? 443 : 80;
  *hostIp = (char *)vbuf;
  char *portB=strchr((char *)vbuf,':');
  *req = strchr((char *)vbuf,'/');
  if(*req != NULL)
  {
    *(*req)=0;
    (*req)++;
  }
  else
  {
    int len=strlen((char *)vbuf);
    *req = (char *)(vbuf + len);
  }
  if(portB != NULL)
  {
     *portB = 0;
     portB++;
     *port = atoi(portB);
     if(port <= 0)
       return false;
  }
  return true;
}
/*
 * It just breaks too many things to allow a stream to go forward without
 * a determined length.  For example: firmware updates, and even at&g returns 
 * a page length for the client.  Let true clients use sockets and handle
 * their own chunked encoding.
class ChunkedStream : public WiFiClient
{
private:
  WiFiClient *wifi = null;
  int chunkCount = 0;
  int chunkSize = 0;
  uint8_t state = 0; //0

public:

    ChunkedStream(WiFiClient *s)
    {
      wifi = s;
    }

    ~ChunkedStream()
    {
      if(wifi != null)
      {
        wifi->stop();
        delete wifi;
      }
    }

    virtual int read()
    {
      if(available()==0)
        return -1;
      char c=wifi->read();
      bool gotC = false;
      int errors = 0;
      while((!gotC) && (errors < 5000))
      {
        switch(state)
        {
          case 0:
            if(c=='0')
              return '\0';
            if((c>='0')&&(c<='9'))
            {
              chunkSize = (c - '0');
              state=1;
            }
            else
            if((c>='a')&&(c<='f'))
            {
              chunkSize = 10 + (c-'a');
              state=1;
            }
            break;
          case 1:
          {
            if((c>='0')&&(c<='9'))
              chunkSize = (chunkSize * 16) + (c - '0');
            else
            if((c>='a')&&(c<='f'))
              chunkSize = (chunkSize * 16) + (c-'a');
            else
            if(c=='\r')
              state=2;
            break;
          }
          case 2:
            if(c == '\n')
            {
              state = 3;
              chunkCount=0;
            }
            else
              state = 0;
            break;
          case 3:
            if(chunkCount < chunkSize)
            {
              gotC = true;
              chunkCount++;
            }
            else
            if(c == '\r')
              state = 4;
            else
              state = 0;
            break;
          case 4:
            if(c == '\n')
              state = 0;
            else
              state = 0; // what else is there to do?!
            break;
        }
        while((!gotC) && (errors < 5000))
        {
            if(available()>0)
            {
              c=wifi->read();
              break;
            }
            else
            if(++errors > 5000)
              break;
            else
              delay(1);
        }
      }
      return c;
    }
    virtual int peek()
    {
      return wifi->peek();
    }

    virtual int read(uint8_t *buf, size_t size)
    {
      if(size == 0)
        return 0;
      int num = available();
      if(num > size)
        num=size;
      for(int i=0;i<num;i++)
        buf[i]=read();
      return num;
    }

    bool getNoDelay()
    {
      return wifi->getNoDelay();
    }
    void setNoDelay(bool nodelay)
    {
      wifi->setNoDelay(nodelay);
    }

    virtual int available()
    {
      return wifi->available();
    }

    virtual void stop()
    {
      wifi->stop();
    }
    virtual uint8_t connected()
    {
      return wifi->connected();
    }
};
 */
WiFiClient *doWebGetStream(const char *hostIp, int port, const char *req, bool doSSL, uint32_t *responseSize)
{
  *responseSize = 0;
  if(WiFi.status() != WL_CONNECTED)
    return null;
  
  WiFiClient *c = createWiFiClient(doSSL);
  if(port == 0)
    port = 80;
  if(!c->connect(hostIp, port))
  {
    c->stop();
    delete c;
    return null;
  }
  c->setNoDelay(DEFAULT_NO_DELAY);

  const char *root = "";
  if(req == NULL)
    req=root;
  if(*req == '/')
    req++;
  
  c->printf("GET /%s HTTP/1.1\r\n",req);
  c->printf("User-Agent: Zimodem Firmware\r\n");
  c->printf("Host: %s\r\n",hostIp);
  c->printf("Connection: close\r\n\r\n");
  
  String ln = "";
  String reUrl = "";
  uint32_t respLength = 0;
  int respCode = -1;
  bool chunked = false;
  while(c->connected() || (c->available()>0))
  {
    yield();
    if(c->available()==0)
      continue;

    char ch = (char)c->read();
    logSocketIn(ch); // this is very much socket input!
    if(ch == '\r')
      continue;
    else
    if(ch == '\n')
    {
      if(ln.length()==0)
        break;
      if(respCode < 0)
      {
        int sp = ln.indexOf(' ');
        if(sp<=0)
          break;
        ln.remove(0,sp+1);
        sp = ln.indexOf(' ');
        if(sp<=0)
          break;
        ln.remove(sp);
        respCode = atoi(ln.c_str());
      }
      else
      {
        int x=ln.indexOf(':');
        if(x>0)
        {
          String header = ln.substring(0,x);
          header.toLowerCase();
          if(header == "content-length")
          {
            ln.remove(0,16);
            respLength = atoi(ln.c_str());
          }
          else
          if(header == "location")
          {
            reUrl = ln;
            reUrl.remove(0,10);
          }
          else
          if(header == "transfer-encoding")
          {
              ln.toLowerCase();
              chunked = ln.indexOf("chunked") > 0;  
          }
        }
      }
      ln = "";
    }
    else
      ln.concat(ch);
  }
  
  if((respCode >= 300) 
  && (respCode <= 399) 
  && (reUrl.length() > 0)
  && (reUrl.length() < 1024))
  {
    char newUrlBuf[reUrl.length()+1];
    strcpy(newUrlBuf,reUrl.c_str());
    char *hostIp2;
    char *req2;
    int port2;
    bool doSSL2;
    if(parseWebUrl((uint8_t *)newUrlBuf, &hostIp2,&req2,&port2,&doSSL2))
    {
        c->stop();
        delete c;
        return doWebGetStream(hostIp2,port2,req2,doSSL2,responseSize);
      
    }
  }
  
  *responseSize = respLength;
  if(((!c->connected())&&(c->available()==0))
  ||(respCode != 200)
  ||(respLength <= 0))
  {
    c->stop();
    delete c;
    return null;
  }
  //if(chunked) // technically, if a length was returned, chunked would be ok, but that's not in the cards.
  //  return new ChunkedStream(c);
  return c;
}

bool doWebGet(const char *hostIp, int port, FS *fs, const char *filename, const char *req, const bool doSSL)
{
  uint32_t respLength=0;
  WiFiClient *c = doWebGetStream(hostIp, port, req, doSSL, &respLength);
  if(c==null)
    return false;
  uint32_t bytesRead = 0;
  File f = fs->open(filename, "w");
  unsigned long now = millis();
  while((bytesRead < respLength) // this can be removed for chunked encoding support 
  && (c->connected()||(c->available()>0)) 
  && ((millis()-now)<10000))
  {
    if(c->available()>0)
    {
      now=millis();
      uint8_t ch=c->read();
      logSocketIn(ch); // this is very much socket input!
      f.write(ch);
      bytesRead++;
    }
    else
      yield();
  }
  f.flush();
  f.close();
  c->stop();
  delete c;
  return (respLength == 0) || (bytesRead == respLength);
}

bool doWebGetBytes(const char *hostIp, int port, const char *req, const bool doSSL, uint8_t *buf, int *bufSize)
{
  *bufSize = -1;
  uint32_t respLength=0;
  WiFiClient *c = doWebGetStream(hostIp, port, req, doSSL, &respLength);
  if(c==null)
    return false;
  if(((!c->connected())&&(c->available()==0))
  ||(respLength > *bufSize))
  {
    c->stop();
    delete c;
    return false;
  }
  *bufSize = (int)respLength;
  int index=0;
  unsigned long now = millis();
  while((index < respLength) // this can be removed for chunked encoding support
  &&(c->connected()||(c->available()>0)) 
  && ((millis()-now)<10000))
  {
    if(c->available()>0)
    {
      uint8_t ch=c->read();
      now = millis();
      logSocketIn(ch); // how is this not socket input -- it's coming from a WiFiClient -- that's THE SOCKET!
      buf[index++] = ch;
    }
    else
      yield();
  }
  *bufSize = index;
  c->stop();
  delete c;
  return (respLength == 0) || (index == respLength);
}
