dabonetn/Link232-Wifi/zimodem/cbm8bit/src/telnetml.asm

        
        
* = 0
        ; .D TELNETML.BIN
        ; TERMINAL ML 64 BY BO ZIMMERMAN
        ; UPDATED 2017/01/01 07:44P
        ; TERMSETUP LDA $DD01:AND #$10:STA DCDCHK
TERMINAL
        LDX #$05
        JSR $FFC6
        JSR $FFE4
        CMP #$00
        BEQ TERMK
        CMP #$0A
        BEQ TERMK
        JSR $FFD2
        ; TERMK LDA $DD01:AND #$10:BNE TERMK2:LDA DCDCHK:BNE ESCOUT
        LDA $029B
        CMP $029C
        BEQ BUFUP
        BCS BUFL1
        LDA #$FF
        SEC
        SBC $029C
        CLC
        ADC $029B
        SEC
        BCS BUFL2
BUFL1   
        SEC
        SBC $029C
BUFL2
        CMP #200
        BCC BUFL3
        LDA $DD01
        AND #$FD
        STA $DD01
        SEC
        BCS TERMK
BUFL3   CMP #20
        BCS TERMK
BUFUP
        LDA $DD01
        ORA #$02
        STA $DD01
TERMK
        LDX #$00
        JSR $FFC6
        JSR $FFE4
        CMP #$00
        BEQ TERMINAL
        CMP #$85
        BEQ ESCOUT
        CMP #$1B
        BNE TERMOUT
ESCOUT
        JSR $FFCC
        RTS
TERMOUT
        PHA
        LDX #$05
        JSR $FFC9
        PLA
        JSR $FFD2
        LDX #$00
        JSR $FFC9
        SEC
        BCS TERMINAL
        ; DCDCHK = $4D
PRINT
        NOP; :F$="TELNETML.BAS":OPEN8,8,15,"S0:TELNETML*":SAVEF$,8:VERIFYF$,8
